VoltaicGRiD/HotHillSideView/hothillsideview46/doc/image/hill46_keys.png

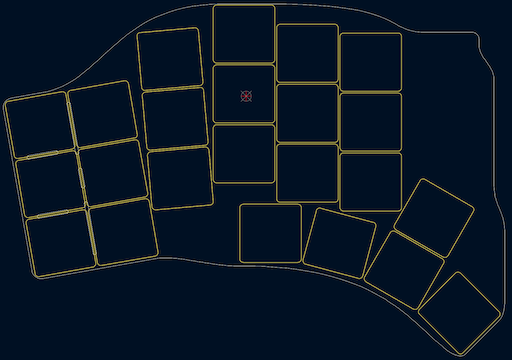
hothillsideview46/doc/image/hill46_keys.png
