VoltaicGRiD/HotHillSideView/hothillsideview46/doc/image/hill46_pcb_render.png

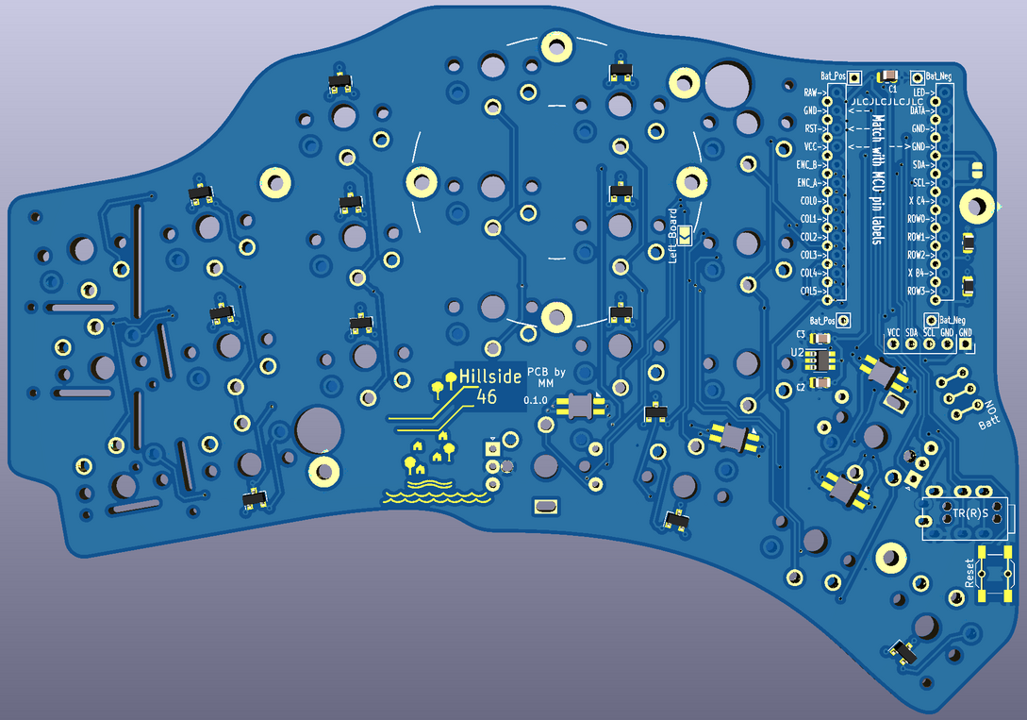
hothillsideview46/doc/image/hill46_pcb_render.png
