VoltaicGRiD/HotHillSideView/hothillsideview46/doc/image/hotswap_on_switch.jpg

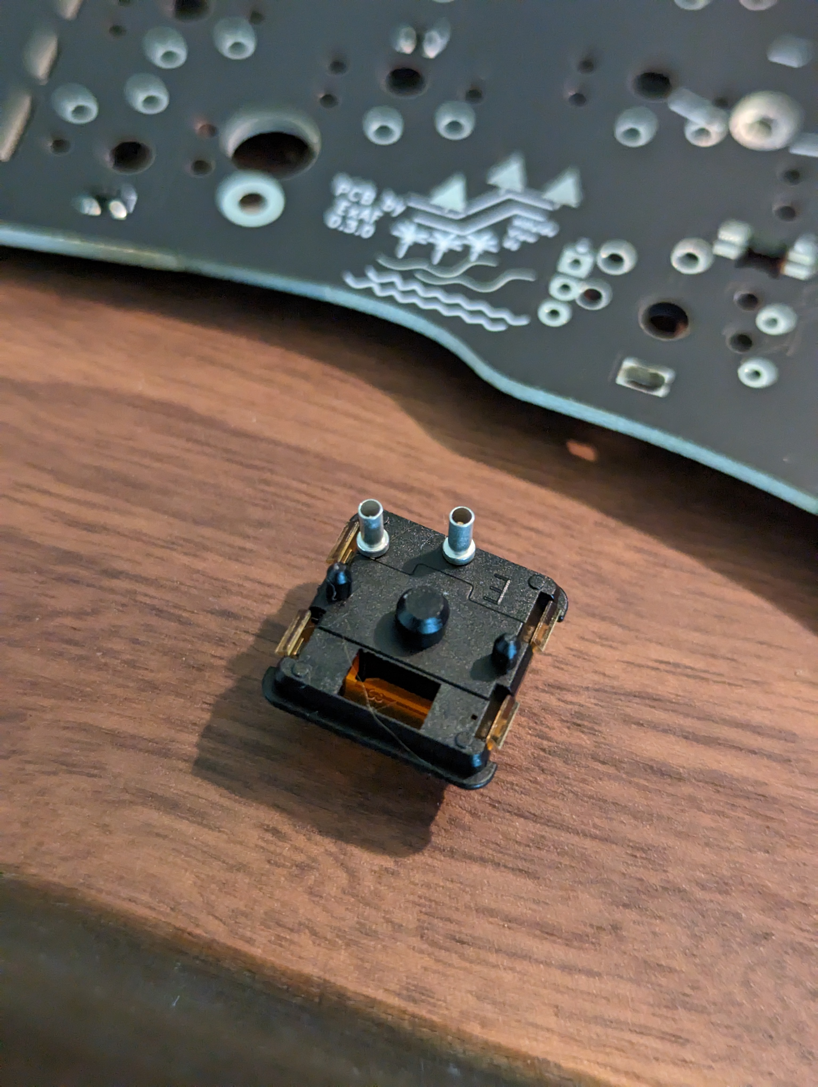
hothillsideview46/doc/image/hotswap_on_switch.jpg
