VoltaicGRiD/HotHillSideView/hothillsideview46/doc/image/hotswap_switch_on_pcb.jpg

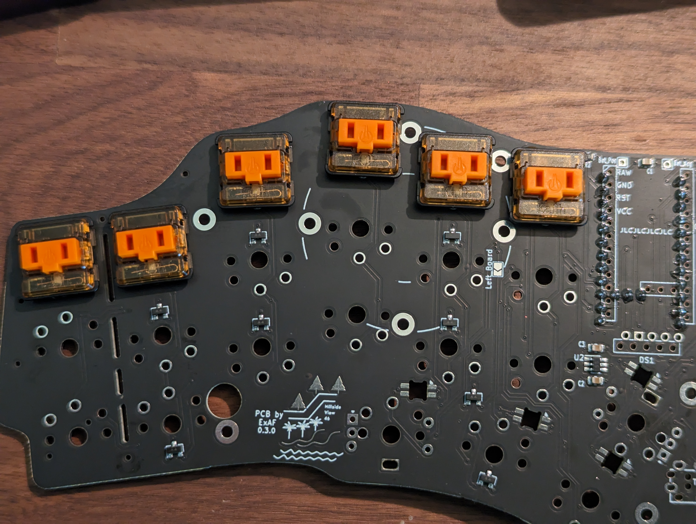
hothillsideview46/doc/image/hotswap_switch_on_pcb.jpg
