VoltaicGRiD/HotHillSideView/hothillsideview46/doc/image/hsv_3x5_chicago_steno.jpg

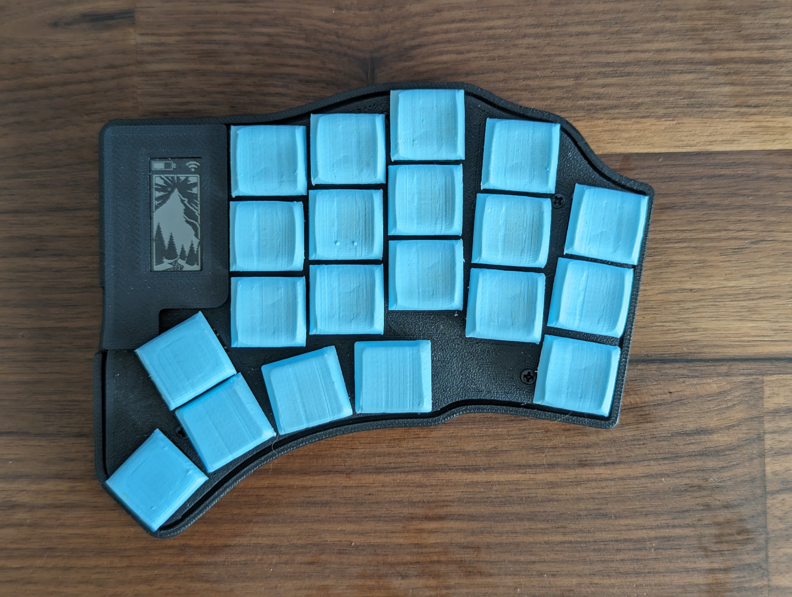
hothillsideview46/doc/image/hsv_3x5_chicago_steno.jpg
