VoltaicGRiD/HotHillSideView/hothillsideview46/doc/image/hsv_3x5_pcb.jpg

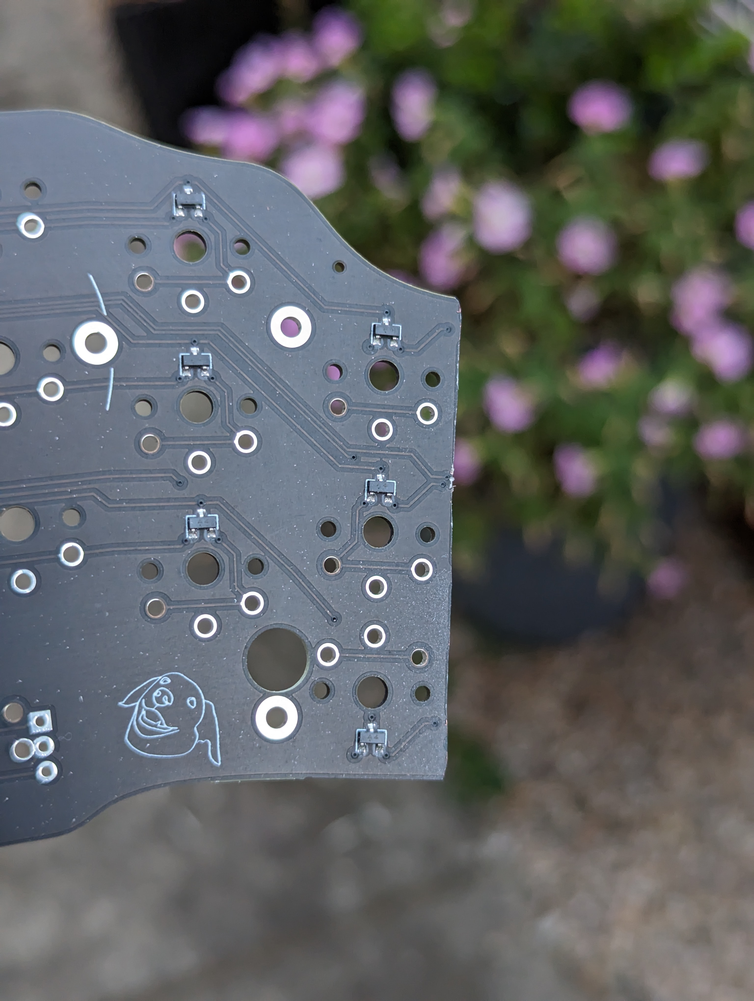
hothillsideview46/doc/image/hsv_3x5_pcb.jpg
