VoltaicGRiD/HotHillSideView/hothillsideview46/doc/image/hsv_display_pcb_mcu_side_view.jpg

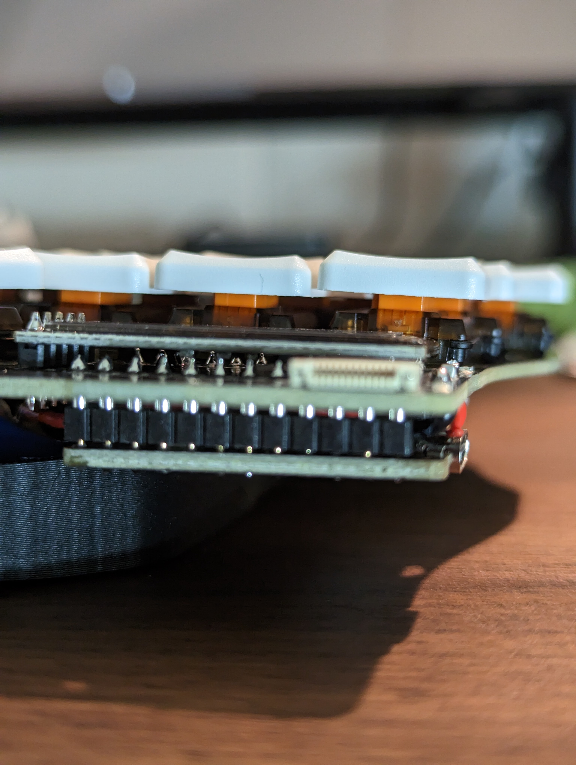
hothillsideview46/doc/image/hsv_display_pcb_mcu_side_view.jpg
