VoltaicGRiD/HotHillSideView/hothillsideview46/doc/image/hsv_klp_lame.jpg

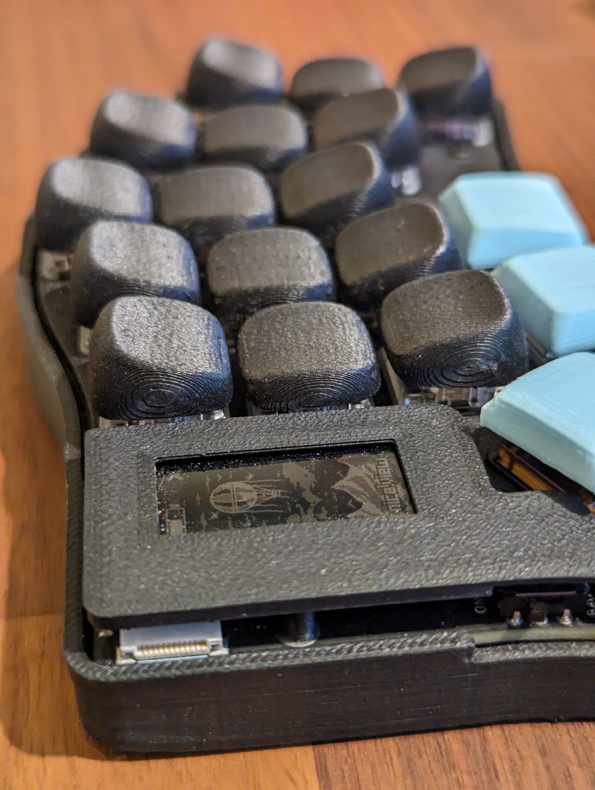
hothillsideview46/doc/image/hsv_klp_lame.jpg
