VoltaicGRiD/HotHillSideView/hothillsideview46/doc/image/hsv_tenting.jpg

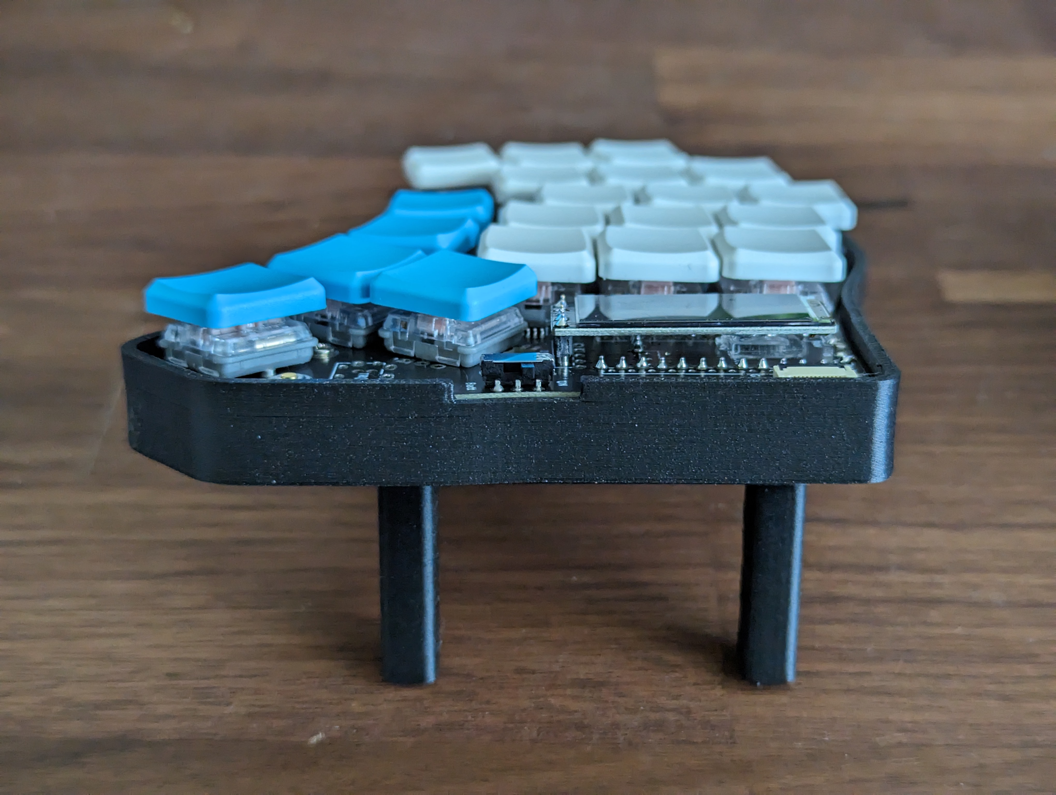
hothillsideview46/doc/image/hsv_tenting.jpg
