VoltaicGRiD/HotHillSideView/hothillsideview46/doc/image/nice_nano_millmax_prep.jpg

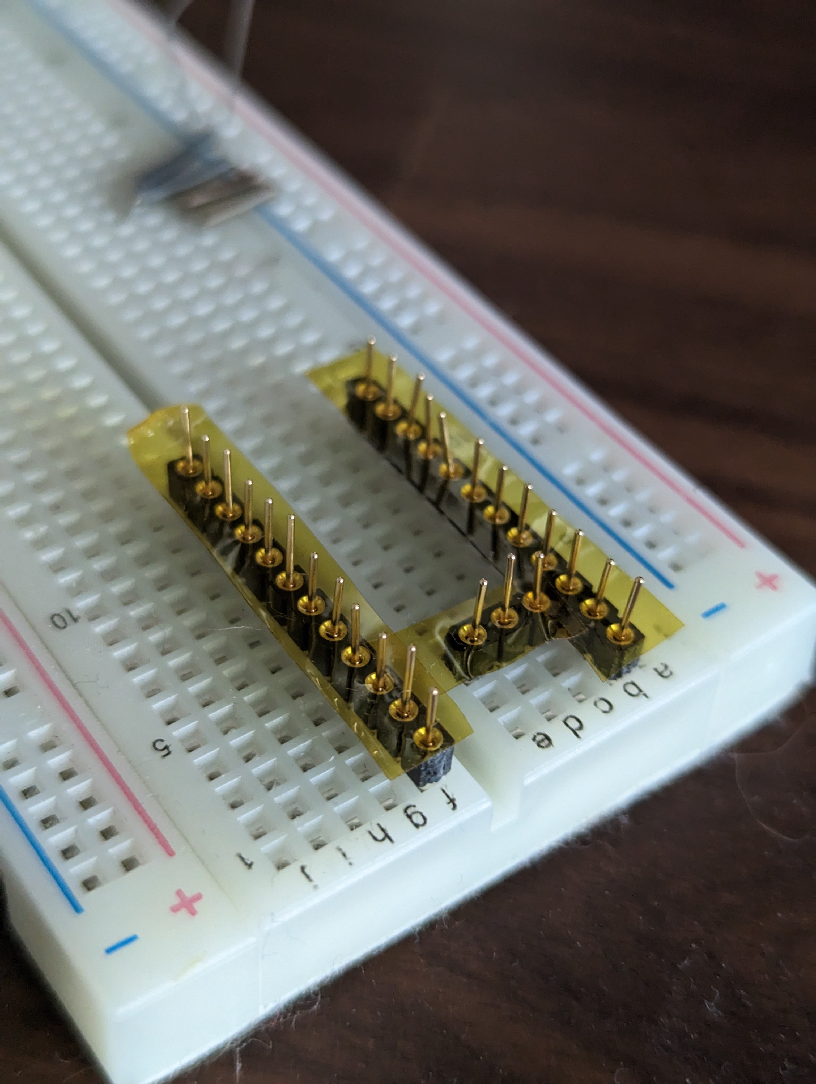
hothillsideview46/doc/image/nice_nano_millmax_prep.jpg
