VoltaicGRiD/HotHillSideView/hothillsideview46/doc/image/battery_soldering.jpg

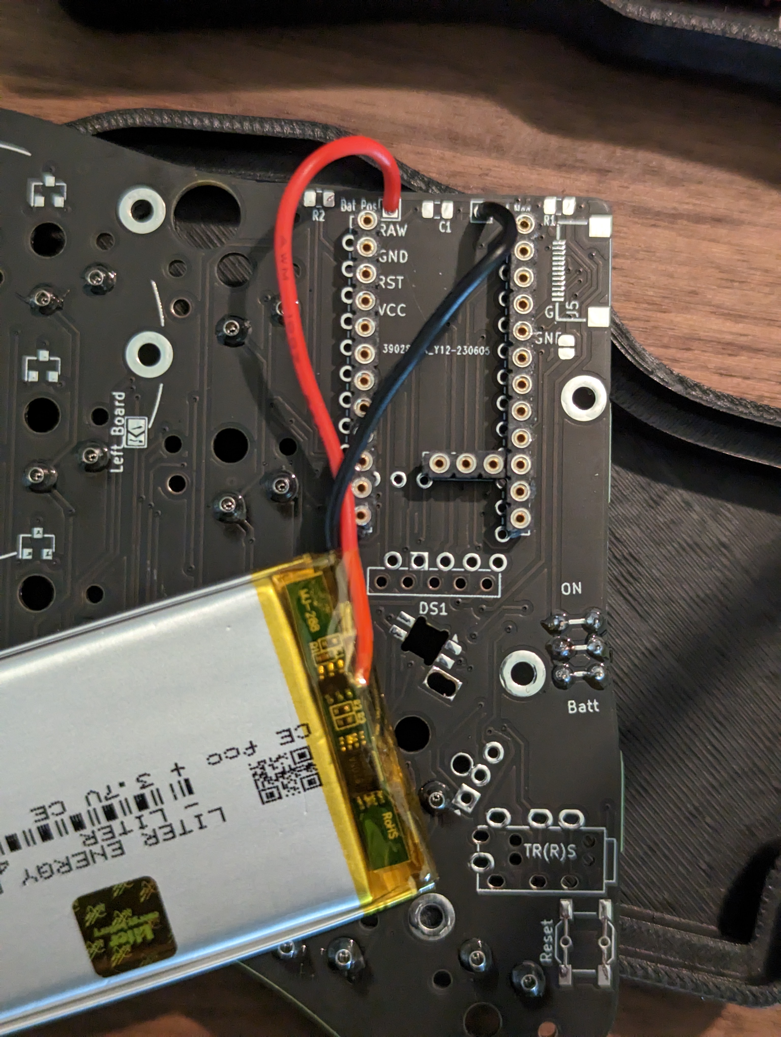
hothillsideview46/doc/image/battery_soldering.jpg
