VoltaicGRiD/HotHillSideView/hothillsideview46/doc/image/hotswap_soldering.jpg

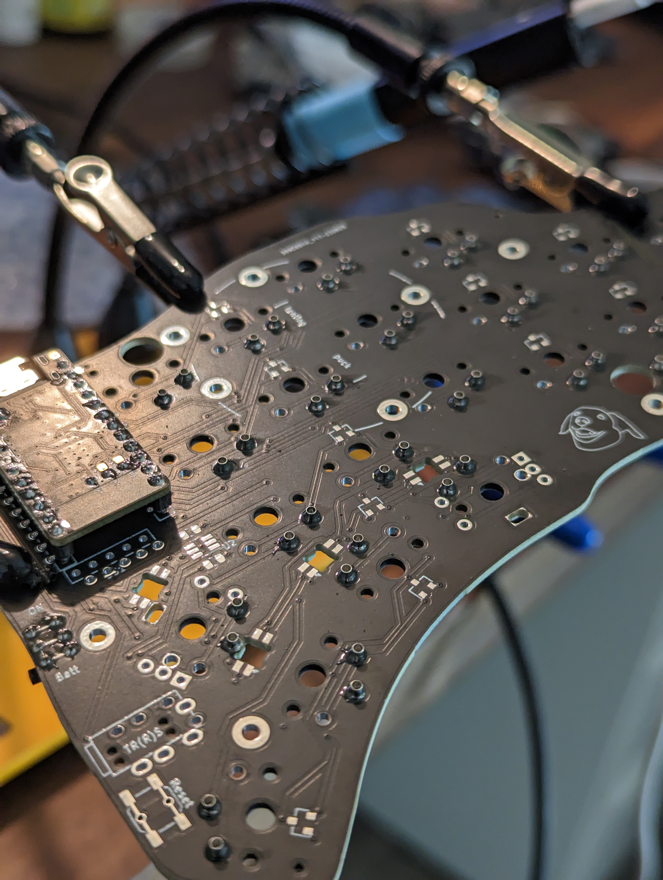
hothillsideview46/doc/image/hotswap_soldering.jpg
