VoltaicGRiD/HotHillSideView/hothillsideview46/doc/image/millmax_soldering.jpg

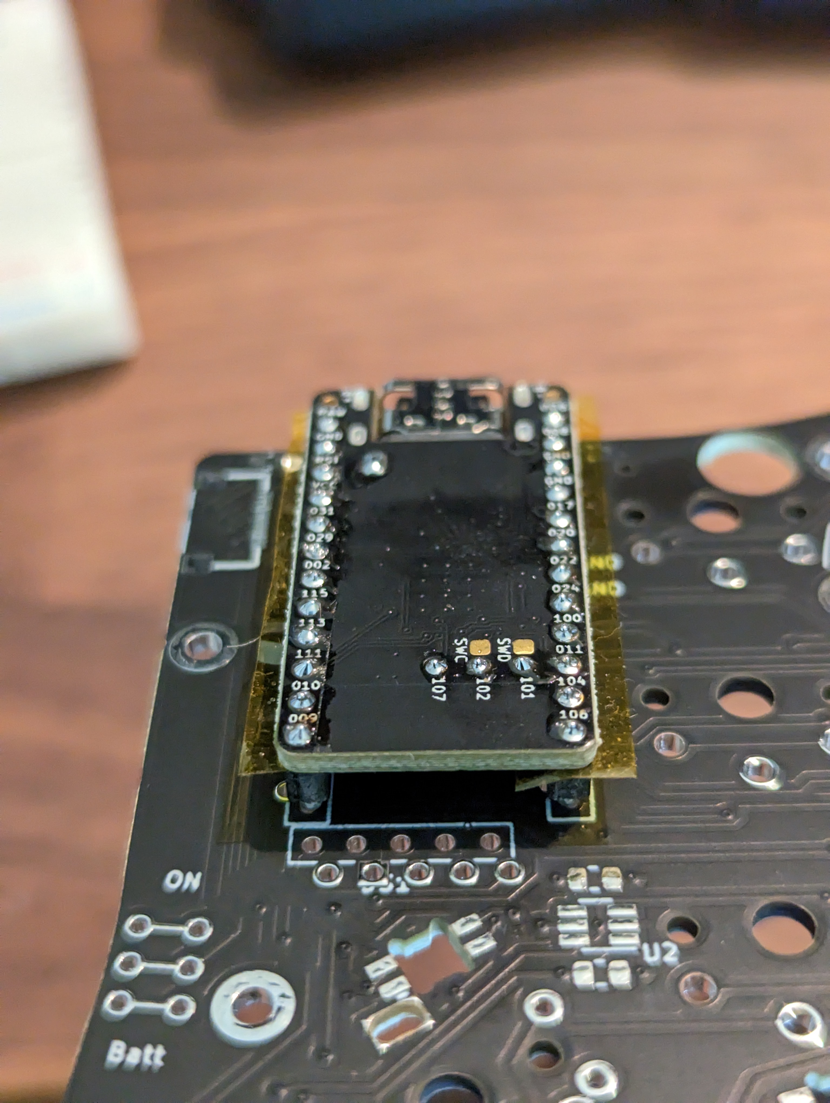
hothillsideview46/doc/image/millmax_soldering.jpg
