VoltaicGRiD/HotHillSideView/hothillsideview46/doc/image/nice_nano_soldering.jpg

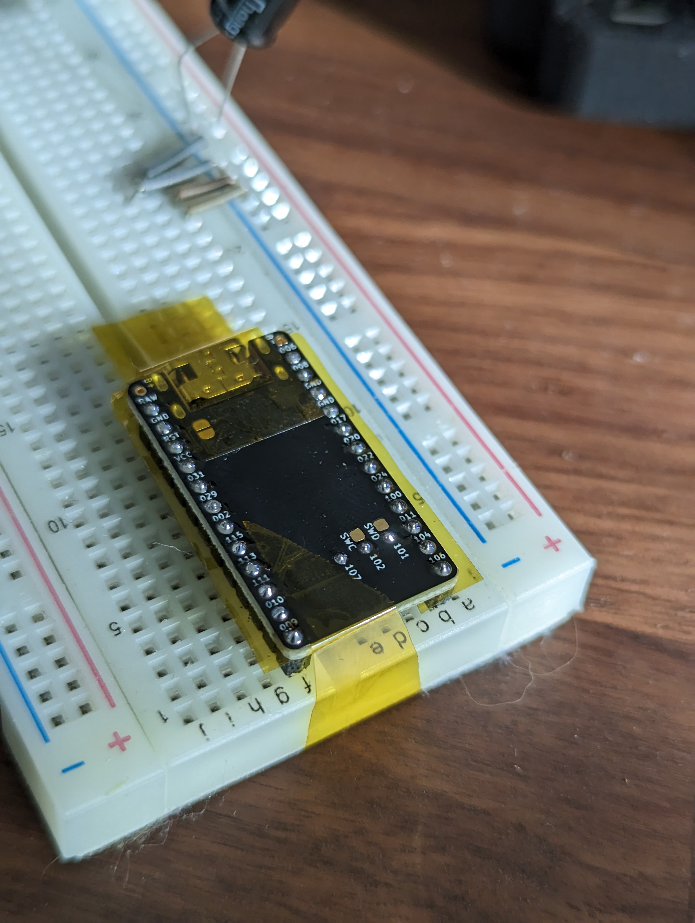
hothillsideview46/doc/image/nice_nano_soldering.jpg
